esl-epfl/CHEEP-boards/main-board/dac_controlled_ldo/power_supply.asc

C1: cap; 1µ; Rser=1.5m
R1: res; 46.4k
R2: res; 48.7k
R3: res; 187k
R8: res; 10K
R9: res; 10K
Rload: res; 1k
U4: LT3062
V2: voltage; PWL(0 2.5 100m 0 200m 2.5)
Vpos: voltage; 3.3
Named nets: 0, OUT, V5, VSENS, VDAC
.tran 200m startup
