esl-epfl/CHEEP-boards/main-board/dac_controlled_ldo/power_supply_opamp.asc

C1: cap; 1µ; Rser=1.5m
R1: res; 105k
R2: res; 127k
R3: res; 649k
R4: res; .1
R8: res; 10K
R9: res; 10K
Rload: res; 10k
U3: ADA4891
U4: LT3062
V2: voltage; PWL(0 0 100m 3.3)
Vpos: voltage; 3.3
Named nets: 0, OUT, V5, VSENS, VBUF, VDAC
.tran 100m startup
