esl-epfl/CHEEP-boards/chewing-gums/PosNegSupply/simulation/lt1118_prog_posneg.asc

C1: polcap; 10µ
D1: TVSdiode; 1N914
R1: res; 53600
R2: res; 53600
R3: res; 11300
RL: res; 1000
U1: LT1118
V1: voltage; 3.3
V2: voltage; 3.3
V3: voltage; PWL(0 1.65 2m 1.65 4m 3.3 6m 3.3 10m 0)
Named nets: 0, vneg, vpos, vdac, vout, vfb
.tran 20m startup
.ic V(vout)=0
